Blinkinlabs/BlinkyTile/tile_pcb/BlinkyTile_panel_1_14.BMP

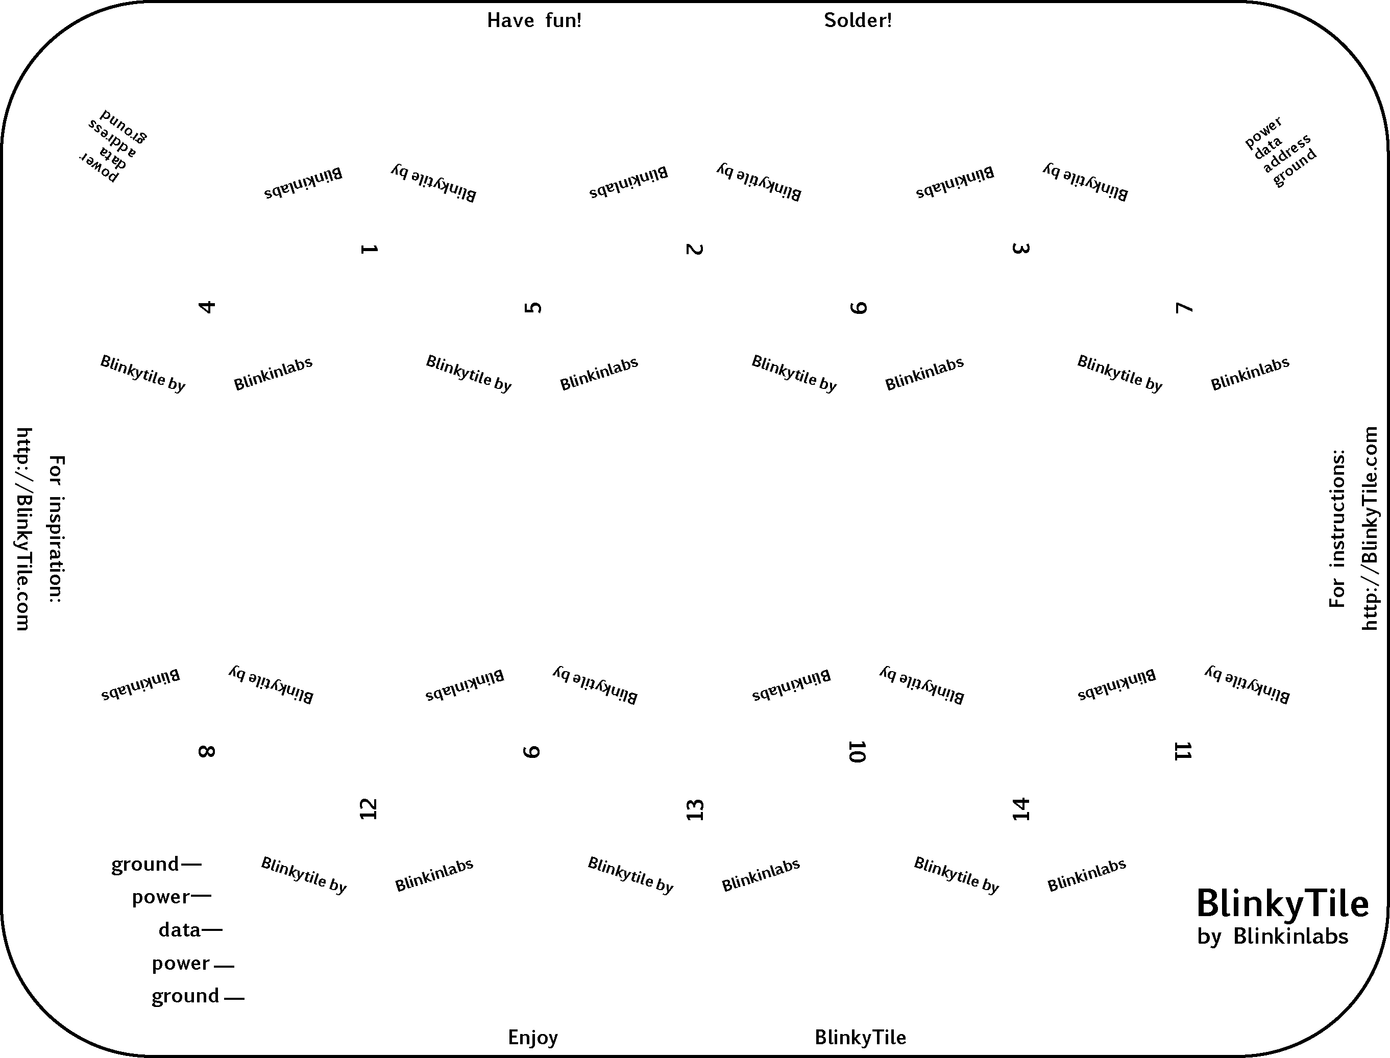
tile_pcb/BlinkyTile_panel_1_14.BMP
